toyi-xing/RV32I/docs/simulation_flow_c.md

# C 仿真流程

本文档说明 RV32I 教学核的 C 裸机测试如何编译、生成 IMEM/DMEM 镜像并通过 Verilator 运行。

---

## 1. 仿真命令

当前仓库统一使用 SoC 仿真入口。旧 core-only testbench 和 `sim/pipeline5_c/` 入口已删除。

```bash
sim/soc_c/run_test.sh <test>
sim/soc_c/run_all.sh
```

`<test>` 可以是四位编号或完整 basename，例如：

```bash
sim/soc_c/run_test.sh 0401
sim/soc_c/run_test.sh 0401_control_mix
```

## 2. 与汇编测试的差异

### 2.1 测试程序结构不同

| | 汇编测试 | C 测试 |
|--|---|---|
| 程序入口 | `sw/asm/<test>.S`，手写 `_start` | `sw/c/<test>.c`，搭配 `sw/c_runtime/crt0.S` |
| 链接脚本 | `sw/linker/asm_test.ld` | `sw/linker/c_baremetal.ld` |
| 内存镜像 | 单文件 `.mem`（只含 imem） | 双文件 `_imem.mem` + `_dmem.mem`（`.dmem_image` 段初始数据） |
| dmem 初始化 | 否（RAM 默认全 0） | 是（C 全局变量初始值通过 dmem 镜像加载） |

### 2.2 仿真命令

C 仿真同时加载 imem 和 dmem：

```bash
Vtb_rv32i_soc "+imem=build/soc_c/<test>_imem.mem" "+dmem=build/soc_c/<test>_dmem.mem"
```

## 3. 可用的 C 测试文件

| 文件 | 描述 | 仿真平台 |
|---|---|---|
| `sw/c/0201_c_smoke.c` | 最小冒烟：1+2=3 自检，通过返回 0 | SoC |
| `sw/c/0202_dmem_init.c` | .rodata/.data/.bss 初始化验证 | SoC |
| `sw/c/0401_control_mix.c` | 嵌套循环冒泡排序、函数调用栈、byte/halfword 访存、分支密集路径 | SoC |
| `sw/c/0551_trap_smoke.c` | C trap handler：ECALL 触发、CSR 读取、mret 返回 | SoC |
| `sw/c/0651_soc_mmio_smoke.c` | GPIO OUT/OE/IN 读写、UART 使能/状态查询/TX 发送 | SoC |
| `sw/c/0652_soc_mmio_gpio_uart.c` | GPIO bit 操作、OUT/OE 独立性与 UART 多字符串 | SoC |
| `sw/c/0751_timer_smoke.c` | TIMER0 machine timer interrupt | SoC |
| `sw/c/0752_gpio_irq_basic.c` | GPIO 四类触发、pending/W1C 与 external interrupt | SoC |
| `sw/c/0753_uart_rx_irq.c` | UART RX 注入、RX interrupt、读清与 W1C | SoC |
| `sw/c/0754_external_timer_priority.c` | MEIP/MTIP 同时 pending 时的优先级 | SoC |
| `sw/c/0757_gpio_periodic_irq.c` | 500/2000 拍 GPIO 周期测量与 4:1 比值 | SoC |
| `sw/c/0853_mmio_wait_basic.c` | 固定 PREADY APB 外设基本读写与副作用 | SoC |
| `sw/c/0856_wait_mixed_random_smoke.c` | AXI-Lite DMEM 与 APB MMIO 混合路由 | SoC |

当前 C 回归共 13 个测试，0836 收口结果为 13 passed、0 failed。

## 4. 新建 C 测试

### 4.1 写 .c 文件

在 `sw/c/` 下新建 `<test>.c`，最小骨架：

```c
int main(void)
{
    // 在这里写测试代码

    return 0;  // 0 表示 PASS；非 0 返回值由 crt0.S 转成 FAIL
}
```

几点说明：

- **入口约定**：`crt0.S` 固定提供 `.text.trap` 入口，同时负责初始化栈指针、清零 `.bss`、加载 `.dmem_image` 到 DMEM 基址，然后调用 `main()`。
- **全局变量初始化**：若 C 测试需要在 DMEM 中预置数据，定义全局变量并赋初值即可。链接脚本会将这些初始值收集到 `.dmem_image` 段，仿真启动时 testbench 通过 `$readmemh` 加载到 `axi_lite_ram.mem`。
- **PASS/FAIL 约定**：C 测试由 `crt0.S` 统一写 `DMEM_BASE + 0x100`（即 `0x00040100`）。`main()` 返回 0 时写 1 表示 PASS，返回非 0 时写 2 表示 FAIL。超时（30010 周期）自动判 TIMEOUT。
- **trap 约定**：需要处理 trap 的 C 测试实现 `__trap_handler_c(unsigned int mcause, unsigned int mepc, unsigned int mtval)`。handler 返回值会写入 `mepc`，随后由 runtime 执行 `mret`；普通 C 测试使用默认弱 handler，若意外 trap 则写 FAIL。
- **MMIO 约定**：需要访问 MMIO 外设的测试包含 `sw/include/platform.h`，使用 `mmio_read32`/`mmio_write32` 等封装函数操作寄存器，且必须在 SoC 仿真平台（`sim/soc_c/`）下运行。

### 4.2 生成 Memory Image

```bash
sim/soc_c/05_build_mem.sh <test>
```

执行流程：

1. `gcc` 编译 + 链接（`-T sw/linker/c_baremetal.ld`）→ `.elf`
2. `objdump -d` → `.dump`
3. `objcopy -j .text.init -j .text.trap -j .text` → `_imem.bin` → `_imem.mem`
4. `objcopy -j .dmem_image` → `_dmem.bin` → `_dmem.mem`

输出在 `build/soc_c/` 下。**每次修改 .c 后都需重新运行此脚本。**

### 4.3 运行仿真

```bash
sim/soc_c/06_run_sim.sh <test>
```

正常输出类似：

```
[0] @ 55: PC=0x00000000 Instr=0x00040537   rd=x10 <= 0x00040000
...
PASS after N cycles
DMEM access range: 0x00040200 - 0x0007fffc
Stack max used:    80 bytes
```

`DMEM access range` 统计仿真期间程序实际发起过 load/store 的最小和最大 DMEM 地址，已排除 `TEST_STATUS_ADDR` 的 PASS/FAIL 写入。`Stack max used` 通过 `min(sp)` 估算最大栈深，C 测试由 `crt0.S` 初始化 `sp`，因此这个值通常比 `.mem` 文件大小更能反映运行时栈压力。DMEM 地址范围不等价于真实 RAM 占用，因为中间地址未必都被访问；详细口径见 `docs/08xx/0827 Testbench、commit trace与测试集组织.md`。

## 5. 调试注意事项

- C 测试的 commit trace 比汇编更晚出现，因为 `crt0.S` 在进入 `main()` 前做了栈和 bss 初始化。
- C trap 测试的 commit trace 会额外看到 `trap_entry/trap_return` 打印，以及 runtime 中保存/恢复寄存器的指令。
- `sw/linker/c_baremetal.ld` 中 `__stack_top` 的值和栈指针初始化代码（`crt0.S`）必须一致，否则 `main()` 内的函数调用会异常。
- 全局变量的 dmem 地址可通过 `.map` 文件或 `.dump` 中的符号地址确认。
- RTL 文件由 SoC 仿真脚本自动收集：`rtl/common/*.sv`、`rtl/core/*.sv`、`rtl/bus/axi_lite/*.sv`、`rtl/bus/bridge/*.sv`、`rtl/bus/apb/*.sv`、`rtl/mem/*.sv`、`rtl/periph/*.sv`、`rtl/soc/*.sv`。
