toyi-xing/RV32I/sw/linker/readme.md

# Linker 与内存分配说明

本文说明当前五级流水线核仿真使用的 IMEM/DMEM 地址图，以及 `asm_test.ld`、`c_baremetal.ld` 的分工。

## 当前地址图

RTL 中当前主线使用 `simple_rom` 作为 IMEM、`axi_lite_ram` 作为 DMEM，两者都使用 32-bit word array。当前 `ADDR_WIDTH=16`，因此每块 memory 有 65536 words，即 256 KiB；`simple_ram` 仅保留为 legacy simple-bus 参考。

| 区域 | 起始地址 | 结束地址 | 大小 | 用途 |
|---|---:|---:|---:|---|
| IMEM | `0x0000_0000` | `0x0003_FFFF` | 256 KiB | 指令、trap handler、部分只读内容 |
| DMEM | `0x0004_0000` | `0x0007_FFFF` | 256 KiB | 数据、测试状态、C 栈 |
| MMIO | `0x0008_0000` | `0x0008_FFFF` | 64 KiB | UART/GPIO/TIMER/ACCEL MMIO window |

MMIO window 内已实现外设（ACCEL0 预留）：

| 外设 | Base | 大小 | 当前状态 |
|---|-----:|----:|---|
| GPIO0 | `0x0008_0000` | 256 B | 已实现 OUT/IN/OE、中断扩展 |
| TIMER0 | `0x0008_1000` | 256 B | 已实现 MTIME/MTIMECMP/CTRL |
| UART0 | `0x0008_2000` | 256 B | 已实现 TXDATA/STATUS/CTRL/RXDATA、中断扩展 |
| ACCEL0 | `0x0008_8000` | 4 KiB | 预留，访问 fault |

对应 RTL 常量在 `rtl/common/core_pkg.sv`（IMEM/DMEM）和 `rtl/common/soc_pkg.sv`（MMIO 窗口）：

```systemverilog
IMEM_BASE       = 32'h0000_0000;
DMEM_BASE       = 32'h0004_0000;
IMEM_SIZE_BYTES = 32'h0004_0000;
DMEM_SIZE_BYTES = 32'h0004_0000;
MTVEC_RESET     = IMEM_BASE + 32'h0000_0080;
```

## IMEM 布局

两个 linker script 都采用同一套 IMEM 入口约定：

| 地址/段 | 用途 |
|---|---|
| `0x0000_0000` / `.text.init` | reset 后第一段代码，必须包含 `_start` |
| `0x0000_0080` / `.text.trap` | M-mode direct trap 入口，对齐 `MTVEC_RESET` |
| `.text` | 普通程序代码，放在 `.text.trap` 之后 |

`.text.trap` 使用 `KEEP(*(.text.trap))`，并且即使当前程序没有 handler，也至少保留 4 bytes。这样普通 `.text` 不会占用 `mtvec` 默认入口；如果程序真的定义了 handler，也不会额外插入无意义占位字。

现有汇编和 C runtime 的 `_start` 都是短入口 stub：

```asm
.section .text.init
_start:
    jal x0, test_main

.section .text
test_main:
    ...
```

这种写法让 reset 入口固定在 `0x0`，同时把普通程序主体避开 `0x80` trap vector。需要 trap handler 的汇编程序应显式放到 `.text.trap`：

```asm
.section .text.trap
trap_handler:
    ...
```

## ASM 链接脚本

`asm_test.ld` 面向手写汇编测试。它的目标是尽量直接、透明：

| 段 | 放置区域 | 说明 |
|---|---|---|
| `.text.init` | IMEM | reset stub |
| `.text.trap` | IMEM `0x80` | trap handler |
| `.text` | IMEM | 普通代码 |
| `.rodata` | IMEM | 只读数据 |
| `.data` | DMEM | 已初始化数据 |
| `.bss` | DMEM | 未初始化数据 |

当前汇编测试优先 `#include "platform.h"` 复用 `DMEM_BASE`、`TEST_STATUS_OFFSET`、外设地址和 CSR bit mask 等公共常量。早期测试可能仍直接用 `lui ..., 0x40` 构造 `DMEM_BASE=0x0004_0000`；这种写法只适合底层冒烟或历史测试，后续新增测试应优先使用公共头文件。

## C 链接脚本

`c_baremetal.ld` 面向 C 裸机测试。C 测试使用两个 memory image：

| 镜像 | 来源段 | 加载目标 |
|---|---|---|
| `_imem.mem` | `.text.init/.text.trap/.text` | `simple_rom` |
| `_dmem.mem` | `.dmem_image` | testbench 中的 `axi_lite_ram.mem` |

C 的 DMEM 布局：

| 地址范围 | 用途 |
|---|---|
| `0x0004_0000` - `0x0004_00FF` | 保留 |
| `0x0004_0100` - `0x0004_0103` | `TEST_STATUS_ADDR` |
| `0x0004_0104` - `0x0004_017F` | 定向测试临时数据/错误码保留区 |
| `0x0004_0180` - `0x0004_018F` | `tb_rv32i_soc.sv` 专用 TB command mailbox |
| `0x0004_0190` - `0x0004_01FF` | 保留 |
| `0x0004_0200` 起 | `.rodata/.data` 初始镜像 |
| `.bss` | `NOLOAD`，由 `crt0.S` 进入 `main()` 前清零 |
| `0x0007_E000` - `0x0007_FFFF` | 预留 C 栈，当前 8 KiB |

关键符号：

| 符号 | 含义 |
|---|---|
| `__test_status_addr` | `DMEM_BASE + 0x100`，`crt0.S` 根据 `main()` 返回值写 PASS/FAIL |
| `__c_data_base` | `DMEM_BASE + 0x200`，C 数据初始镜像起点 |
| `__stack_top` | `DMEM_BASE + DMEM_SIZE_BYTES = 0x0008_0000` |
| `__stack_size` | 当前固定为 `0x2000` |
| `__stack_bottom` | `__stack_top - __stack_size = 0x0007_E000` |
| `__trap_vector` | `IMEM_BASE + 0x80` |

`crt0.S` 使用 linker symbol 设置 `sp`、清零 `.bss`，然后调用 `main()`。C 程序自身不应直接写 `TEST_STATUS_ADDR`；它只返回 0 或非 0，由 `crt0.S` 统一写状态字。

C runtime 还固定提供 `.text.trap` 入口。该入口保存寄存器、读取 `mcause/mepc/mtval`，调用弱符号 `__trap_handler_c`，再按 handler 返回值写 `mepc` 并执行 `mret`。普通 C 测试不触发 trap 时不会用到它；需要处理 trap 的测试提供同名强定义即可覆盖默认 FAIL handler。

`TB_CMD_BASE = DMEM_BASE + 0x180` 及其后 16 bytes 只属于当前 `tb/sv/tb_rv32i_soc.sv` 的 directed-test mailbox 协议，不是真实 SoC 地址图，也不属于通用外设 MMIO ABI。当前四个 word 分别用于 GPIO set、GPIO clear、GPIO pulse 和 UART RX；`0x0004_0190` 起不再定义旧 response-delay 命令。具体地址和 helper 定义见 `sw/include/tb_rv32i_soc_test.h`。

## 修改地址图时要同步的地方

如果后续继续调整 IMEM/DMEM 大小或基址，需要一起检查：

- `rtl/common/core_pkg.sv` 的 `IMEM_*`、`DMEM_*` 常量。
- `rtl/mem/simple_rom.sv`、`rtl/mem/axi_lite_ram.sv` 的默认 `ADDR_WIDTH` 是否仍引用公共常量；`simple_ram.sv` 只在 legacy simple-bus 场景需要同步。
- `sw/linker/asm_test.ld` 和 `sw/linker/c_baremetal.ld` 的 `MEMORY`、`__stack_top`、`__test_status_addr` 等符号。
- `sw/include/platform.h` 中的软件侧地址常量；若仍有历史手写汇编直接构造地址，也需要同步检查。
- `sw/include/tb_rv32i_soc_test.h` 中 TB mailbox 地址是否仍落在 linker 保留区内。
- `tb/sv/tb_rv32i_soc.sv` 中 PASS/FAIL 地址和 DMEM/stack 统计。
- `docs/simulation_flow_asm.md` / `docs/simulation_flow_c.md` 中的命令示例和地址说明。
