toyi-xing/RV32I/fpga/fpga_e10_board_resources/3_正点原子E10最小系统板原理图/readme.txt

E10最小系统板IO引脚分配表：E10最小系统板管脚IO引脚分配表
E10_MicroSYS_IO：E10最小系统板TCL格式IO引脚分配，在工程中做IO分配时，可以直接从该文件中拷贝（要注意该TCL文件的端口名称和工程里的端口名是否一致）
E10最小系统板原理图：E10最小系统板原理图

本目录下包含了正点原子E10最小系统板的所有电路原理图,有的文档有多页,请滚动鼠标滚轮查看!!!

		广州市星翼电子科技有限公司
            电话：020-38271790
            传真：020-36773971
	       	购买：http://shop62103354.taobao.com
                  http://shop62057469.taobao.com
            公司网站：www.alientek.com
         	技术论坛：www.openedv.com
