toyi-xing/RV32I/docs/08xx/0821 RV32I最小教学核指令集、编码与译码参考.md

# 0821 RV32I 最小教学核指令集、编码与译码参考

> 文档编号：0821  
> 所属系列：082x RISC-V 最小教学核项目实践  
> 文档定位：第一版 RV32I 教学核的指令、编码、立即数和译码控制参考  
> 前置文档：`0801 RISC-V ISA基础.md`、`0802 RISC-V五级流水线与Hazard.md`、`0820 RISC-V最小教学核设计流程与方案.md`

本文不是完整 RISC-V 规范替代品，而是为了写第一版 RV32I 五级流水线教学核时查表使用。目标是让实现者能快速回答：

1. 第一版到底支持哪些指令。
2. 每条指令属于哪种 type。
3. opcode、funct3、funct7 怎么匹配。
4. 哪些指令读 `rs1/rs2`，哪些指令写 `rd`。
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
