toyi-xing/RV32I/rtl/core/core.sv

//------------------------------------------------------------------------------
// 文件      : rtl/core/core.sv
// 用途      : RV32I 五级流水线教学核顶层。
//
// 综合PPA：
//   - 该顶层使用 yosys 综合器 + 浙芯 55nm 开源工艺库综合结果：
//   - 最终面积 28351.40，其中时序单元 16896.04 (59.60%)
//   - Setup (max) Worst Slack = 17.569 ns  理论上可以跑到 ~411MHz
//   - Hold (min) Worst Slack = 0.125 ns
//   - Total Power = 0.445 W
//
// 规范：
//   - 普通输入端口使用 _i 后缀，普通输出端口使用 _o 后缀。
//   - commit_instr_id_o 为仿真 trace 观察口，沿用 commit_* 分组命名。
//   - 本模块实现 IF/ID/EX/MEM/WB 五级流水线顶层连接。
//   - 外接 imem 和 LSU 数据侧接口，不在 core 内部实例化具体 memory。
//   - 当前 IMEM 仍为固定响应；LSU 数据侧使用单 outstanding req/resp 结构体接口。
//
// 功能：
//   - 连接 pc_reg、if_stage、id_stage、ex_stage、mem_stage、wb_stage、regfile、csr_file 和 trap_ctrl。
//   - 使用 pipeline_pkg 中的 struct 描述四组流水线寄存器承载的数据和控制。
//   - 处理 forwarding、load-use/CSR-use stall 和 branch/JAL/JALR redirect flush。
//   - 支持 MEM backpressure，IMEM 固定响应。
//   - 在 MEM 边界精确接受 trap/MRET，并通过 kill 清除 younger instruction 或终止当前 MEM 指令普通 WB 路径。
//   - 输出 commit trace 和 trap/MRET trace 观察信号，供 testbench 打印和调试使用。
//------------------------------------------------------------------------------

`default_nettype none

module core (
    input  logic                          clk_i,
    input  logic                          rst_n_i,

    input  logic [core_pkg::ILEN-1:0]     imem_rdata_i,         // imem 返回的 32 bit instruction。
    output logic [core_pkg::XLEN-1:0]     imem_addr_o,          // 输出给 imem 的取指地址。

    // 可变延迟访存总线
    input  logic                          lsu_req_ready_i,          // data-side 可以接受本拍 request；valid && !ready 时 MEM 需要保持等待。
    output data_bus_pkg::data_req_t       lsu_req_o,                // LSU load/store request payload。
    input  data_bus_pkg::data_resp_t      lsu_resp_i,               // LSU response，包含 valid/rdata/error。

    // 中断信号输入
    input  logic                          mtip_i,               // 外设的 mtip 中断挂起
    input  logic                          meip_i,               // 外设的 meip 中断挂起

    // WB 指令提交观察
    output logic                          commit_valid_o,       // 当前拍是否有有效指令提交。
    output logic [core_pkg::XLEN-1:0]     commit_pc_o,          // 提交指令的 PC。
    output logic [core_pkg::ILEN-1:0]     commit_instr_o,       // 提交指令的原始 instruction。
    output core_pkg::instr_id_e           commit_instr_id_o,    // 提交指令类型
    output logic                          commit_reg_we_o,      // 提交指令是否写 rd。
    output logic [4:0]                    commit_rd_addr_o,     // 提交指令写回的 rd 编号。
    output logic [core_pkg::XLEN-1:0]     commit_rd_wdata_o,    // 提交指令写回 rd 的数据。

    // trap/MRET 提交观察
    output logic                          trap_valid_o,         // trap entry 有效（异常/中断），不含 MRET。
    output logic [core_pkg::XLEN-1:0]     trap_pc_o,            // 写入 mepc 的 PC；exception 时为 fault PC，interrupt 时为 return PC。
    output logic                          trap_is_interrupt_o,  // 该 trap 是中断。
    output logic [4:0]                    trap_cause_code_o,    // 当前 trap entry 的 cause code，配合 trap_is_interrupt_o 区分异常和中断。
    output logic [core_pkg::XLEN-1:0]     trap_tval_o,          // 异常相关附加值（mtval 写入值）。
    output logic                          trap_return_o,        // MRET 返回事件有效。
    output logic [core_pkg::XLEN-1:0]     trap_redirect_pc_o,   // trap 或 MRET 的跳转目标 PC。

    // 流水线暂停观察
    output logic                          mem_wait_o            // 因 mem wait 导致的流水线暂停
);
    import core_pkg::*;
    import pipeline_pkg::*;
    import data_bus_pkg::*;

    // pc相关信号
    wire [core_pkg::XLEN-1:0] pc;
    wire                      ex_redirect_valid;
    wire [core_pkg::XLEN-1:0] ex_redirect_pc;
    wire                      nontrap_redirect_valid;
    wire [core_pkg::XLEN-1:0] nontrap_redirect_pc;
    wire                      trap_redirect_valid;
    wire [core_pkg::XLEN-1:0] trap_redirect_pc;
    wire                      redirect_valid = trap_redirect_valid | nontrap_redirect_valid;
    wire [core_pkg::XLEN-1:0] redirect_pc    = trap_redirect_valid ? trap_redirect_pc : nontrap_redirect_pc;

    // pipeline_ctrl 输出的非 trap 类 stall/bubble。
    wire stall_pc;
    wire stall_if_id;
    wire stall_id_ex;
    wire stall_ex_mem;
    wire stall_mem_wb;
    wire bubble_ex;

    // pipeline_ctrl 输出普通 redirect flush；trap/MRET kill 由 trap_ctrl 输出。
    wire flush_if_id;
    wire flush_id_ex;

    // trap/MRET kill 信号
    wire kill_if_id;
    wire kill_id_ex;
    wire kill_ex_mem;
    wire kill_mem_wb;

    // 各 valid 信号，中间 data。由中间寄存器寄存
    wire pc_valid;
    wire if_valid, if_id_valid;
    wire id_valid, id_ex_valid;
    wire ex_valid, ex_mem_valid;
    wire mem_valid, mem_wb_valid, mem_wb_commit_valid;
    wire wb_valid;
    pipeline_pkg::if_id_reg_t if_id_data_d;
    pipeline_pkg::if_id_reg_t if_id_data_q;
    pipeline_pkg::id_ex_reg_t id_ex_data_d;
    pipeline_pkg::id_ex_reg_t id_ex_data_q;
    pipeline_pkg::ex_mem_reg_t ex_mem_data_d;
    pipeline_pkg::ex_mem_reg_t ex_mem_data_q;
    pipeline_pkg::mem_wb_reg_t mem_wb_data_d;
    pipeline_pkg::mem_wb_reg_t mem_wb_data_q;

    // GPR
    wire [4:0]                id_rs1_addr;
    wire [4:0]                id_rs2_addr;
    wire [core_pkg::XLEN-1:0] gpr_rs1_rdata;
    wire [core_pkg::XLEN-1:0] gpr_rs2_rdata;
    wire [core_pkg::XLEN-1:0] wb_rd_wdata;
    wire                      wb_rd_we;

    // IF
    wire [core_pkg::XLEN-1:0] if_pc;
    wire [core_pkg::ILEN-1:0] if_instr;
    wire [core_pkg::XLEN-1:0] if_pc_plus4;

    // ID
    wire [4:0]                id_rd_addr;
    wire                      id_uses_rs1;
    wire                      id_uses_rs2;
    wire                      id_illegal_instr;
    core_pkg::alu_op_e        id_alu_op;
    core_pkg::op_a_sel_e      id_op_a_sel;
    core_pkg::op_b_sel_e      id_op_b_sel;
    wire                      id_rd_we;
    core_pkg::wb_sel_e        id_wb_sel;
    wire                      id_mem_re;
    wire                      id_mem_we;
    core_pkg::mem_size_e      id_mem_size;
    wire                      id_mem_unsigned;
    core_pkg::branch_op_e     id_branch_op;
    wire                      id_jump;
    wire                      id_jalr;
    wire [core_pkg::XLEN-1:0] id_imm;
    wire [core_pkg::XLEN-1:0] id_rs1_rdata, id_rs2_rdata;
    core_pkg::instr_id_e      id_instr_id;
    wire                      id_fence;
    wire                      id_mret;
    wire                      id_csr;
    core_pkg::csr_op_e        id_csr_op;
    wire [11:0]               id_csr_addr;
    wire [4:0]                id_csr_uimm;
    wire                      id_csr_uses_rs1;
    wire                      id_csr_writes_rd;
    wire                      id_csr_write_en;
    wire                      id_exception_valid;
    core_pkg::excp_cause_e    id_exception_cause;
    wire [core_pkg::XLEN-1:0] id_exception_tval;

    // forwarding 前递结果 -> EX 操作数
    wire [core_pkg::XLEN-1:0] ex_rs1_op_data;
    wire [core_pkg::XLEN-1:0] ex_rs2_op_data;

    // EX
    wire [core_pkg::XLEN-1:0] ex_alu_result;
    wire [core_pkg::XLEN-1:0] ex_store_data;
    wire                      ex_exception_valid;
    core_pkg::excp_cause_e    ex_exception_cause;
    wire [core_pkg::XLEN-1:0] ex_exception_tval;
    wire [core_pkg::XLEN-1:0] ex_csr_operand;
    wire                      ex_mret;
    wire [core_pkg::XLEN-1:0] ex_next_pc;

    // MEM
    wire                      mem_wait;
    wire [core_pkg::XLEN-1:0] mem_load_data;
    wire                      mem_exception_valid;
    core_pkg::excp_cause_e    mem_exception_cause;
    wire [core_pkg::XLEN-1:0] mem_exception_tval;

    // CSR 信号
    wire                      mem_csr_valid;    // 当前 MEM 阶段的 csr 指令控制信号
    wire [core_pkg::XLEN-1:0] mem_csr_rdata;
    wire                      mem_csr_illegal;
    wire [core_pkg::XLEN-1:0] csr_mstatus;
    wire [core_pkg::XLEN-1:0] csr_mstatus_commit;
    wire [core_pkg::XLEN-1:0] csr_mie;
    wire [core_pkg::XLEN-1:0] csr_mie_commit;
    wire [core_pkg::XLEN-1:0] csr_mtvec;        // 恒为当前对于 csr 寄存器值
    wire [core_pkg::XLEN-1:0] csr_mtvec_commit;
    wire [core_pkg::XLEN-1:0] csr_mepc;
    wire [core_pkg::XLEN-1:0] csr_mip;

    // 系统级 trap 信号
    wire                      trap_valid;
    wire [core_pkg::XLEN-1:0] trap_pc;
    wire                      trap_is_interrupt;
    wire [4:0]                trap_cause_code;
    wire [core_pkg::XLEN-1:0] trap_tval;
    wire                      mret_valid;

    // WB 随指令输出 -> commit
    wire [core_pkg::ILEN-1:0] wb_instr          = mem_wb_data_q.instr;
    core_pkg::instr_id_e      wb_instr_id;
    assign                    wb_instr_id       = mem_wb_data_q.instr_id;
    wire [core_pkg::XLEN-1:0] wb_pc             = mem_wb_data_q.pc;
    wire [4:0]                wb_rd_addr        = mem_wb_data_q.rd_addr;

    pc_reg u_pc_reg(
        .clk_i              (clk_i),
        .rst_n_i            (rst_n_i),

        .pc_plus4_i         (if_pc_plus4),
        .redirect_pc_i      (redirect_pc),
        .redirect_valid_i   (redirect_valid),
        .stall_pc_i         (stall_pc), // if 要 stall 一拍，让 pc 保持不变

        .pc_o               (pc),
        .pc_valid_o         (pc_valid)
    );

    if_stage u_if_stage (
        .pc_i           (pc),
        .imem_rdata_i   (imem_rdata_i),
        .pc_valid_i     (pc_valid),

        .imem_addr_o    (imem_addr_o),
        .if_pc_o        (if_pc),
        .if_pc_plus4_o  (if_pc_plus4),
        .if_instr_o     (if_instr),
        .if_valid_o     (if_valid)
    );

    pipe_reg_if_id u_pipe_reg_if_id (
        .clk_i      (clk_i),
        .rst_n_i    (rst_n_i),

        .data_i     (if_id_data_d),
        .valid_i    (if_valid),
        .kill_i     (kill_if_id),       // trap control hazard
        .flush_i    (flush_if_id),      // base control hazard
        .stall_i    (stall_if_id),      // late_result_use_stall 时 id 要 stall 一拍

        .data_o     (if_id_data_q),
        .valid_o    (if_id_valid)
    );

    // IF/ID 输入组包。后续若取指侧增加 kill/valid 修正，在这里改。
    assign if_id_data_d.pc       = if_pc;
    assign if_id_data_d.instr    = if_instr;
    assign if_id_data_d.pc_plus4 = if_pc_plus4;

    id_stage u_id_stage (
        .if_valid_i     (if_id_valid),
        .if_instr_i     (if_id_data_q.instr),
        .rs1_rdata_i    (gpr_rs1_rdata),
        .rs2_rdata_i    (gpr_rs2_rdata),

        .rs1_addr_o     (id_rs1_addr),
        .rs2_addr_o     (id_rs2_addr),
        .rd_addr_o      (id_rd_addr),

        .instr_id_o     (id_instr_id),     // 调试用,送到流水线结束

        .uses_rs1_o     (id_uses_rs1),
        .uses_rs2_o     (id_uses_rs2),

        .alu_op_o       (id_alu_op),
        .op_a_sel_o     (id_op_a_sel),
        .op_b_sel_o     (id_op_b_sel),

        .reg_we_o       (id_rd_we),
        .wb_sel_o       (id_wb_sel),

        .mem_re_o       (id_mem_re),
        .mem_we_o       (id_mem_we),
        .mem_size_o     (id_mem_size),
        .mem_unsigned_o (id_mem_unsigned),

        .branch_op_o    (id_branch_op),

        .jump_o         (id_jump),
        .jalr_o         (id_jalr),
        .fence_o        (id_fence),
        .mret_o         (id_mret),

        .csr_o              (id_csr),
        .csr_op_o           (id_csr_op),
        .csr_addr_o         (id_csr_addr),
        .csr_uimm_o         (id_csr_uimm),
        .csr_uses_rs1_o     (id_csr_uses_rs1),
        .csr_writes_rd_o    (id_csr_writes_rd),     // csr 指令写 gpr
        .csr_write_en_o     (id_csr_write_en),      // csr 指令写 csr

        .exception_valid_o  (id_exception_valid),
        .exception_cause_o  (id_exception_cause),
        .exception_tval_o   (id_exception_tval),

        .illegal_instr_o(id_illegal_instr),

        .id_imm_o       (id_imm),

        .id_valid_o     (id_valid),
        .id_rs1_rdata_o (id_rs1_rdata),
        .id_rs2_rdata_o (id_rs2_rdata)
    );

    regfile #(.BYPASS_EN(1)) u_regfile (
        .clk_i          (clk_i),
        .rst_n_i        (rst_n_i),

        .rs1_addr_i     (id_rs1_addr),
        .rs1_rdata_o    (gpr_rs1_rdata),

        .rs2_addr_i     (id_rs2_addr),
        .rs2_rdata_o    (gpr_rs2_rdata),

        .we_i           (wb_rd_we),
        .rd_addr_i      (wb_rd_addr),
        .rd_wdata_i     (wb_rd_wdata)
    );

    // forwarding，处理 RAW 时 EX/MEM -> EX 和 MEM/WB -> EX
    forwarding_unit u_forwarding_unit (
        .id_ex_valid_i      (id_ex_valid),
        .id_ex_rs1_addr_i   (id_ex_data_q.rs1_addr),
        .id_ex_rs2_addr_i   (id_ex_data_q.rs2_addr),
        .id_ex_uses_rs1_i   (id_ex_data_q.uses_rs1),
        .id_ex_uses_rs2_i   (id_ex_data_q.uses_rs2),

        .ex_mem_valid_i     (ex_mem_valid),
        .ex_mem_rd_addr_i   (ex_mem_data_q.rd_addr),
        .ex_mem_reg_we_i    (ex_mem_data_q.reg_we),
        .ex_mem_load_re_i   (ex_mem_data_q.mem_re),
        .ex_mem_csr_re_i    (ex_mem_data_q.csr_writes_rd),

        .mem_wb_valid_i     (mem_wb_valid),
        .mem_wb_rd_addr_i   (mem_wb_data_q.rd_addr),
        .mem_wb_reg_we_i    (mem_wb_data_q.reg_we),

        .id_ex_rs1_rdata_i  (id_ex_data_q.rs1_rdata),
        .id_ex_rs2_rdata_i  (id_ex_data_q.rs2_rdata),
        .ex_mem_wb_sel_i    (ex_mem_data_q.wb_sel),
        .ex_mem_alu_result_i(ex_mem_data_q.alu_result),
        .ex_mem_pc_plus4_i  (ex_mem_data_q.pc_plus4),
        .ex_mem_imm_i       (ex_mem_data_q.imm),
        .mem_wb_wdata_i     (wb_rd_wdata),

        .rs1_fwd_o          (ex_rs1_op_data),
        .rs2_fwd_o          (ex_rs2_op_data)
    );

    pipe_reg_id_ex u_pipe_reg_id_ex (
        .clk_i      (clk_i),
        .rst_n_i    (rst_n_i),

        .data_i     (id_ex_data_d),
        .valid_i    (id_valid),
        .kill_i     (kill_id_ex),     // trap control hazard
        .flush_i    (flush_id_ex),    // base control hazard
        .bubble_i   (bubble_ex),
        .stall_i    (stall_id_ex),

        .data_o     (id_ex_data_q),
        .valid_o    (id_ex_valid)
    );

    // ID/EX 输入组包。控制信号从 ID 生成，随指令进入 EX。
    assign id_ex_data_d.rs1_addr      = id_rs1_addr;
    assign id_ex_data_d.rs2_addr      = id_rs2_addr;
    assign id_ex_data_d.uses_rs1      = id_uses_rs1;
    assign id_ex_data_d.uses_rs2      = id_uses_rs2;
    assign id_ex_data_d.illegal_instr = id_illegal_instr;
    assign id_ex_data_d.instr_id      = id_instr_id;

    assign id_ex_data_d.rd_addr       = id_rd_addr;
    assign id_ex_data_d.alu_op        = id_alu_op;
    assign id_ex_data_d.op_a_sel      = id_op_a_sel;
    assign id_ex_data_d.op_b_sel      = id_op_b_sel;
    assign id_ex_data_d.reg_we        = id_rd_we;
    assign id_ex_data_d.wb_sel        = id_wb_sel;
    assign id_ex_data_d.mem_re        = id_mem_re;
    assign id_ex_data_d.mem_we        = id_mem_we;
    assign id_ex_data_d.mem_size      = id_mem_size;
    assign id_ex_data_d.mem_unsigned  = id_mem_unsigned;
    assign id_ex_data_d.branch_op     = id_branch_op;
    assign id_ex_data_d.jump          = id_jump;
    assign id_ex_data_d.jalr          = id_jalr;
    assign id_ex_data_d.imm           = id_imm;
    assign id_ex_data_d.rs1_rdata     = id_rs1_rdata;
    assign id_ex_data_d.rs2_rdata     = id_rs2_rdata;

    assign id_ex_data_d.pc            = if_id_data_q.pc;        // 此类为中间寄存器直接透传
    assign id_ex_data_d.pc_plus4      = if_id_data_q.pc_plus4;
    assign id_ex_data_d.instr         = if_id_data_q.instr;

    assign id_ex_data_d.exception_valid = id_exception_valid;
    assign id_ex_data_d.exception_cause = id_exception_cause;
    assign id_ex_data_d.exception_tval  = id_exception_tval;
    assign id_ex_data_d.fence           = id_fence;
    assign id_ex_data_d.mret            = id_mret;
    assign id_ex_data_d.csr             = id_csr;
    assign id_ex_data_d.csr_op          = id_csr_op;
    assign id_ex_data_d.csr_addr        = id_csr_addr;
    assign id_ex_data_d.csr_uimm        = id_csr_uimm;
    assign id_ex_data_d.csr_uses_rs1    = id_csr_uses_rs1;
    assign id_ex_data_d.csr_writes_rd   = id_csr_writes_rd;
    assign id_ex_data_d.csr_write_en    = id_csr_write_en;

    ex_stage u_ex_stage (
        .valid_i            (id_ex_valid),

        .pc_i               (id_ex_data_q.pc),
        .pc_plus4_i         (id_ex_data_q.pc_plus4),
        .rs1_data_i         (ex_rs1_op_data),
        .rs2_data_i         (ex_rs2_op_data),
        .imm_i              (id_ex_data_q.imm),
        .alu_op_i           (id_ex_data_q.alu_op),
        .op_a_sel_i         (id_ex_data_q.op_a_sel),
        .op_b_sel_i         (id_ex_data_q.op_b_sel),
        .branch_op_i        (id_ex_data_q.branch_op),
        .jump_i             (id_ex_data_q.jump),
        .jalr_i             (id_ex_data_q.jalr),

        .exception_valid_i  (id_ex_data_q.exception_valid),
        .exception_cause_i  (id_ex_data_q.exception_cause),
        .exception_tval_i   (id_ex_data_q.exception_tval),
        .csr_i              (id_ex_data_q.csr),
        .csr_op_i           (id_ex_data_q.csr_op),
        .csr_uimm_i         (id_ex_data_q.csr_uimm),
        .mret_i             (id_ex_data_q.mret),

        .valid_o            (ex_valid),
        .alu_result_o       (ex_alu_result),
        .store_data_o       (ex_store_data),
        .redirect_valid_o   (ex_redirect_valid),
        .redirect_pc_o      (ex_redirect_pc),

        .exception_valid_o  (ex_exception_valid),
        .exception_cause_o  (ex_exception_cause),
        .exception_tval_o   (ex_exception_tval),
        .csr_operand_o      (ex_csr_operand),
        .mret_o             (ex_mret),
        .next_pc_o          (ex_next_pc)
    );

    pipe_reg_ex_mem u_pipe_reg_ex_mem (
        .clk_i      (clk_i),
        .rst_n_i    (rst_n_i),

        .data_i     (ex_mem_data_d),
        .valid_i    (ex_valid),
        .kill_i     (kill_ex_mem),     // trap control hazard
        .stall_i    (stall_ex_mem),

        .data_o     (ex_mem_data_q),
        .valid_o    (ex_mem_valid)
    );

    // EX/MEM 输入组包。EX 结果和仍需后传的控制信号在这里汇总。
    assign ex_mem_data_d.illegal_instr = id_ex_data_q.illegal_instr;    // 此类为中间寄存器透传
    assign ex_mem_data_d.instr_id      = id_ex_data_q.instr_id;

    assign ex_mem_data_d.alu_result    = ex_alu_result;     // 此类为上一阶段结果
    assign ex_mem_data_d.store_data    = ex_store_data;

    assign ex_mem_data_d.mem_re        = id_ex_data_q.mem_re;
    assign ex_mem_data_d.mem_we        = id_ex_data_q.mem_we;
    assign ex_mem_data_d.mem_size      = id_ex_data_q.mem_size;
    assign ex_mem_data_d.mem_unsigned  = id_ex_data_q.mem_unsigned;
    assign ex_mem_data_d.wb_sel        = id_ex_data_q.wb_sel;
    assign ex_mem_data_d.reg_we        = id_ex_data_q.reg_we;
    assign ex_mem_data_d.pc_plus4      = id_ex_data_q.pc_plus4;
    assign ex_mem_data_d.imm           = id_ex_data_q.imm;
    assign ex_mem_data_d.rd_addr       = id_ex_data_q.rd_addr;
    assign ex_mem_data_d.instr         = id_ex_data_q.instr;
    assign ex_mem_data_d.pc            = id_ex_data_q.pc;

    assign ex_mem_data_d.exception_valid = ex_exception_valid;
    assign ex_mem_data_d.exception_cause = ex_exception_cause;
    assign ex_mem_data_d.exception_tval  = ex_exception_tval;
    assign ex_mem_data_d.fence           = id_ex_data_q.fence;
    assign ex_mem_data_d.mret            = ex_mret;
    assign ex_mem_data_d.csr             = id_ex_data_q.csr;
    assign ex_mem_data_d.csr_op          = id_ex_data_q.csr_op;
    assign ex_mem_data_d.csr_addr        = id_ex_data_q.csr_addr;
    assign ex_mem_data_d.csr_operand     = ex_csr_operand;
    assign ex_mem_data_d.csr_writes_rd   = id_ex_data_q.csr_writes_rd;
    assign ex_mem_data_d.csr_write_en    = id_ex_data_q.csr_write_en;
    assign ex_mem_data_d.next_pc         = ex_next_pc;

    mem_stage u_mem_stage (
        .clk_i                  (clk_i),
        .rst_n_i                (rst_n_i),

        .valid_i                (ex_mem_valid),
        .alu_result_i           (ex_mem_data_q.alu_result),
        .store_data_i           (ex_mem_data_q.store_data),
        .mem_re_i               (ex_mem_data_q.mem_re),
        .mem_we_i               (ex_mem_data_q.mem_we),
        .mem_size_i             (ex_mem_data_q.mem_size),
        .mem_unsigned_i         (ex_mem_data_q.mem_unsigned),

        .valid_o                (mem_valid),
        .load_data_o            (mem_load_data),

        .exception_valid_i      (ex_mem_data_q.exception_valid),
        .exception_cause_i      (ex_mem_data_q.exception_cause),
        .exception_tval_i       (ex_mem_data_q.exception_tval),

        .exception_valid_o      (mem_exception_valid),
        .exception_cause_o      (mem_exception_cause),
        .exception_tval_o       (mem_exception_tval),

        .lsu_req_ready_i        (lsu_req_ready_i),
        .lsu_req_o              (lsu_req_o),
        .lsu_resp_i             (lsu_resp_i),

        .mem_wait_o             (mem_wait),

        .mem_misaligned_o       (),     // 可作为调试信号使用，暂不接
        .load_misaligned_o      (),
        .store_misaligned_o     (),
        .mem_access_fault_o     (),
        .load_access_fault_o    (),
        .store_access_fault_o   (),
        .transaction_complete_o (),
        .mem_complete_o         ()
    );

    // 与 mem_stage “并连”,mem_valid 只是防御性写法，实际上 CSR 指令与访存指令互斥，用 ex_mem_valid 也可且可能更快
    assign mem_csr_valid = mem_valid & ex_mem_data_q.csr & ~mem_exception_valid;
    csr_file u_csr_file (
        .clk_i              (clk_i),
        .rst_n_i            (rst_n_i),

        .csr_valid_i        (mem_csr_valid),
        .csr_op_i           (ex_mem_data_q.csr_op),
        .csr_addr_i         (ex_mem_data_q.csr_addr),
        .csr_operand_i      (ex_mem_data_q.csr_operand),
        .csr_write_en_i     (ex_mem_data_q.csr_write_en),

        .csr_rdata_o        (mem_csr_rdata),
        .csr_illegal_o      (mem_csr_illegal),

        .trap_valid_i       (trap_valid),
        .trap_pc_i          (trap_pc),
        .trap_is_interrupt_i(trap_is_interrupt),
        .trap_cause_code_i  (trap_cause_code),
        .trap_tval_i        (trap_tval),

        .mret_valid_i       (mret_valid),

        .mtip_i             (mtip_i),
        .meip_i             (meip_i),

        .mstatus_o          (csr_mstatus),
        .mstatus_commit_o   (csr_mstatus_commit),
        .mie_o              (csr_mie),
        .mie_commit_o       (csr_mie_commit),
        .mtvec_o            (csr_mtvec),
        .mtvec_commit_o     (csr_mtvec_commit),
        .mepc_o             (csr_mepc),
        .mip_o              (csr_mip)
    );

    trap_ctrl u_trap_ctrl (
        .mem_valid_i                (mem_valid),                // 访存完成后才能明确且允许 trap
        .mem_pc_i                   (ex_mem_data_q.pc),         // 本指令的 pc
        .mem_instr_i                (ex_mem_data_q.instr),
        .mem_mret_i                 (ex_mem_data_q.mret),

        .mem_exception_valid_i      (mem_exception_valid),
        .mem_exception_cause_i      (mem_exception_cause),
        .mem_exception_tval_i       (mem_exception_tval),

        .mem_csr_valid_i            (mem_csr_valid),
        .mem_csr_illegal_i          (mem_csr_illegal),

        .csr_mtvec_i                (csr_mtvec),
        .csr_mepc_i                 (csr_mepc),

        .mem_interrupt_return_pc_i  (ex_mem_data_q.next_pc),    // 本指令的下一个 pc
        .csr_mstatus_i              (csr_mstatus),
        .csr_mie_i                  (csr_mie),
        .csr_mip_i                  (csr_mip),
        .mem_csr_write_en_i         (ex_mem_data_q.csr_write_en),
        .csr_mstatus_commit_i       (csr_mstatus_commit),
        .csr_mie_commit_i           (csr_mie_commit),
        .csr_mtvec_commit_i         (csr_mtvec_commit),

        .trap_valid_o               (trap_valid),
        .trap_pc_o                  (trap_pc),      // 写入 mepc 的 PC：exception 为 fault PC，interrupt 为 return PC。
                                                    // 普通 interrupt 使用 next_pc，MRET+interrupt 使用当前 mepc。
        .trap_is_interrupt_o        (trap_is_interrupt),
        .trap_cause_code_o          (trap_cause_code),
        .trap_tval_o                (trap_tval),

        .mret_valid_o               (mret_valid),

        .redirect_valid_o           (trap_redirect_valid),
        .redirect_pc_o              (trap_redirect_pc),

        .kill_if_id_o               (kill_if_id),
        .kill_id_ex_o               (kill_id_ex),
        .kill_ex_mem_o              (kill_ex_mem),
        .kill_mem_wb_o              (kill_mem_wb)
    );

    // trap/MRET 随流水线在 MEM 边界精确提交，这里只把观察信号导出给 testbench。
    assign trap_valid_o         = trap_valid;
    assign trap_pc_o            = trap_pc;
    assign trap_is_interrupt_o  = trap_is_interrupt;
    assign trap_cause_code_o    = trap_cause_code;
    assign trap_tval_o          = trap_tval;
    assign trap_return_o        = mret_valid;
    assign trap_redirect_pc_o   = trap_redirect_pc;

    // pipeline_ctrl 统一整合 late-result-use stall、non-trap redirect flush 和 MEM backpressure。
    pipeline_ctrl u_pipeline_ctrl (
        .if_id_valid_i              (if_id_valid),
        .id_rs1_addr_i              (id_rs1_addr),
        .id_rs2_addr_i              (id_rs2_addr),
        .id_uses_rs1_i              (id_uses_rs1),
        .id_uses_rs2_i              (id_uses_rs2),

        .id_ex_valid_i              (id_ex_valid),
        .id_ex_rd_addr_i            (id_ex_data_q.rd_addr),
        .id_ex_reg_we_i             (id_ex_data_q.reg_we),
        .id_ex_load_re_i            (id_ex_data_q.mem_re),
        .id_ex_csr_re_i             (id_ex_data_q.csr_writes_rd),

        .mem_wait_i                 (mem_wait),

        .ex_redirect_valid_i        (ex_redirect_valid),
        .ex_redirect_pc_i           (ex_redirect_pc),

        .nontrap_redirect_valid_o   (nontrap_redirect_valid),
        .nontrap_redirect_pc_o      (nontrap_redirect_pc),

        .stall_pc_o                 (stall_pc),
        .stall_if_id_o              (stall_if_id),
        .stall_id_ex_o              (stall_id_ex),
        .stall_ex_mem_o             (stall_ex_mem),
        .stall_mem_wb_o             (stall_mem_wb),

        .bubble_ex_o                (bubble_ex),
        .flush_if_id_o              (flush_if_id),
        .flush_id_ex_o              (flush_id_ex)
    );

    pipe_reg_mem_wb u_pipe_reg_mem_wb (
        .clk_i          (clk_i),
        .rst_n_i        (rst_n_i),

        .data_i         (mem_wb_data_d),
        .valid_i        (mem_valid),
        .kill_i         (kill_mem_wb),     // trap control hazard，终止该指令生命周期（已被 trap 提交）
        .stall_i        (stall_mem_wb),    // MEM wait 还要 stall MEM/WB，供 forwarding 的 MEM/WB -> EX，但续额外处理重复提交问题

        .data_o         (mem_wb_data_q),
        .valid_o        (mem_wb_valid),
        .commit_valid_o (mem_wb_commit_valid)   // 一次有效指令只能提交一次
    );

    // MEM/WB 输入组包。WB 使用这里保存的最终写回选择和数据。
    assign mem_wb_data_d.illegal_instr = ex_mem_data_q.illegal_instr;
    assign mem_wb_data_d.instr_id      = ex_mem_data_q.instr_id;

    assign mem_wb_data_d.load_data     = mem_load_data;

    assign mem_wb_data_d.reg_we        = ex_mem_data_q.reg_we;
    assign mem_wb_data_d.wb_sel        = ex_mem_data_q.wb_sel;
    assign mem_wb_data_d.alu_result    = ex_mem_data_q.alu_result;
    assign mem_wb_data_d.pc_plus4      = ex_mem_data_q.pc_plus4;
    assign mem_wb_data_d.imm           = ex_mem_data_q.imm;
    assign mem_wb_data_d.rd_addr       = ex_mem_data_q.rd_addr;
    assign mem_wb_data_d.instr         = ex_mem_data_q.instr;
    assign mem_wb_data_d.pc            = ex_mem_data_q.pc;

    assign mem_wb_data_d.csr_rdata     = mem_csr_rdata;

    wb_stage u_wb_stage (
        .valid_i        (mem_wb_commit_valid),  // 指令一旦流入 wb 阶段比被提交，因此副作用、提交 valid 需要用脉冲 mem_wb_commit_valid
        .reg_we_i       (mem_wb_data_q.reg_we),
        .rd_addr_i      (mem_wb_data_q.rd_addr),
        .wb_sel_i       (mem_wb_data_q.wb_sel),
        .alu_result_i   (mem_wb_data_q.alu_result),
        .load_data_i    (mem_wb_data_q.load_data),
        .pc_plus4_i     (mem_wb_data_q.pc_plus4),
        .imm_i          (mem_wb_data_q.imm),
        .csr_rdata_i    (mem_wb_data_q.csr_rdata),

        .valid_o        (wb_valid),
        .reg_we_o       (wb_rd_we),
        .wb_wdata_o     (wb_rd_wdata)
    );

    assign commit_valid_o    = wb_valid;
    assign commit_pc_o       = wb_pc;
    assign commit_instr_o    = wb_instr;
    assign commit_instr_id_o = wb_instr_id;
    assign commit_reg_we_o   = wb_rd_we;
    assign commit_rd_addr_o  = wb_rd_addr;
    assign commit_rd_wdata_o = wb_rd_wdata;

    assign mem_wait_o = mem_wait;

endmodule

`default_nettype wire
