toyi-xing/RV32I/rtl/soc/rv32i_soc.sv

//------------------------------------------------------------------------------
// 文件      : rtl/soc/rv32i_soc.sv
// 用途      : RV32I 教学核最小 SoC 平台顶层。
//
// 规范：
//   - 普通输入端口使用 _i 后缀，普通输出端口使用 _o 后缀。
//   - 本模块集成固定响应 IMEM、core-side simple data bus 和 AXI-Lite/APB 数据子系统。
//   - CPU core、外置 IMEM、外置 AXI-Lite DMEM 和内部 APB MMIO 外设在本层连接。
//   - data 观察口按 request/response 结构体分组，避免混淆 request 意图和 response completion。
//
// 功能：
//   - 实例化 core 作为 CPU core。
//   - 透出固定响应 IMEM 端口，由 testbench 或上层 wrapper 连接 simple_rom/ROM model。
//   - 实例化 data_subsystem，把 core simple request 路由到外置 AXI-Lite DMEM 或内部 APB 外设。
//   - 将 data_subsystem response valid/rdata/error 接回 core LSU response 端口。
//   - 汇总 GPIO0/UART0 中断为 MEIP，将 TIMER0 中断作为 MTIP 接入 core。
//   - 透传 commit/trap、GPIO、UART、interrupt 和 data access 观察信号给 testbench。
//------------------------------------------------------------------------------

`default_nettype none

module rv32i_soc (
    input  logic                          clk_i,
    input  logic                          rst_n_i,

    output logic [core_pkg::XLEN-1:0]     imem_addr_o,           // 取指 byte address，连接外置固定响应 IMEM。
    input  logic [core_pkg::ILEN-1:0]     imem_rdata_i,          // 外置 IMEM 返回的 instruction。

    // ----------------------------以下连接外置 DMEM 和外设激励-----------------------------------
    output axi_lite_pkg::axi_lite_req_t   dmem_axi_req_o,        // 发往外置 DMEM AXI-Lite slave 的 request。
    input  axi_lite_pkg::axi_lite_resp_t  dmem_axi_resp_i,       // 外置 DMEM AXI-Lite slave 的 response。

    input  logic [31:0]                   gpio0_in_i,            // GPIO0 输入引脚采样值。
    output logic [31:0]                   gpio0_out_o,           // GPIO0 输出寄存器值。
    output logic [31:0]                   gpio0_oe_o,            // GPIO0 输出使能寄存器值。

    output logic                          uart0_tx_valid_o,      // UART0 TX event 有效脉冲。
    output logic [7:0]                    uart0_tx_data_o,       // UART0 TX event 对应字节。
    input  logic                          uart0_rx_valid_i,      // UART0 RX event 脉冲。
    input  logic [7:0]                    uart0_rx_data_i,       // UART0 RX event 对应字节。

    // ----------------------------以下为 commit/观察口-----------------------------------------
    // data request/response 观察口；load/store 既可能访问 DMEM，也可能访问外设寄存器。
    output logic                          data_req_ready_o,      // data-side 握手：本拍可接受 request。
    output data_bus_pkg::data_req_t       data_req_o,            // core 发起的 LSU request。
    output data_bus_pkg::data_resp_t      data_resp_o,           // data-side response。


    output logic                          dmem_access_o,         // 本拍 data access 是否命中 DMEM。
    output logic                          mmio_access_o,         // 本拍 data access 是否命中已实现 MMIO。
    output logic                          undefined_access_o,    // 本拍 data access 是否命中未实现或未映射区域。

    // 指令提交
    output logic                          commit_valid_o,        // 当前拍是否有有效指令提交。
    output logic [core_pkg::XLEN-1:0]     commit_pc_o,           // 提交指令的 PC。
    output logic [core_pkg::ILEN-1:0]     commit_instr_o,        // 提交指令的原始 instruction。
    output core_pkg::instr_id_e           commit_instr_id_o,     // 提交指令类型。
    output logic                          commit_reg_we_o,       // 提交指令是否写 rd。
    output logic [4:0]                    commit_rd_addr_o,      // 提交指令写回的 rd 编号。
    output logic [core_pkg::XLEN-1:0]     commit_rd_wdata_o,     // 提交指令写回 rd 的数据。

    // trap 提交
    output logic                          trap_valid_o,          // trap entry 有效（异常/中断），不含 MRET。
    output logic [core_pkg::XLEN-1:0]     trap_pc_o,             // 发生异常/中断时的指令 PC。
    output logic                          trap_is_interrupt_o,   // 该 trap 是中断。
    output logic [4:0]                    trap_cause_code_o,     // 当前 trap entry 的 cause code，配合 trap_is_interrupt_o 区分异常和中断。
    output logic [core_pkg::XLEN-1:0]     trap_tval_o,           // 异常相关附加值。
    output logic                          trap_return_o,         // MRET 返回事件有效。
    output logic [core_pkg::XLEN-1:0]     trap_redirect_pc_o,    // trap 或 MRET 的跳转目标 PC。

    // 流水线暂停观察
    output logic                          mem_wait_o,            // 因 mem wait 导致的流水线暂停

    // 中断观察
    output logic                          gpio0_irq_o,           // GPIO0 中断。
    output logic                          uart0_irq_o,           // UART0 中断。
    output logic                          timer0_irq_o,          // TIMER0 中断（MTIP）。
    output logic                          meip_o,                // MEIP = gpio0_irq_o | uart0_irq_o。
    output logic                          mtip_o                 // MTIP = timer0_irq_o。
);
    import data_bus_pkg::*;

    // interrupt 汇总
    wire   meip   = gpio0_irq_o | uart0_irq_o;
    wire   mtip   = timer0_irq_o;
    assign meip_o = meip;
    assign mtip_o = mtip;

    core u_core (
        .clk_i                  (clk_i),
        .rst_n_i                (rst_n_i),

        .imem_rdata_i           (imem_rdata_i),
        .imem_addr_o            (imem_addr_o),

        .lsu_req_ready_i        (data_req_ready_o),
        .lsu_req_o              (data_req_o),
        .lsu_resp_i             (data_resp_o),

        .mtip_i                 (mtip),
        .meip_i                 (meip),

        .commit_valid_o         (commit_valid_o),
        .commit_pc_o            (commit_pc_o),
        .commit_instr_o         (commit_instr_o),
        .commit_instr_id_o      (commit_instr_id_o),
        .commit_reg_we_o        (commit_reg_we_o),
        .commit_rd_addr_o       (commit_rd_addr_o),
        .commit_rd_wdata_o      (commit_rd_wdata_o),

        .trap_valid_o           (trap_valid_o),
        .trap_pc_o              (trap_pc_o),
        .trap_is_interrupt_o    (trap_is_interrupt_o),
        .trap_cause_code_o      (trap_cause_code_o),
        .trap_tval_o            (trap_tval_o),
        .trap_return_o          (trap_return_o),
        .trap_redirect_pc_o     (trap_redirect_pc_o),

        .mem_wait_o             (mem_wait_o)
    );

    data_subsystem u_data_subsystem (
        .clk_i                 (clk_i),
        .rst_n_i               (rst_n_i),

        .core_req_ready_o      (data_req_ready_o),
        .core_req_i            (data_req_o),
        .core_resp_o           (data_resp_o),

        .dmem_axi_req_o        (dmem_axi_req_o),
        .dmem_axi_resp_i       (dmem_axi_resp_i),

        .gpio0_in_i            (gpio0_in_i),
        .gpio0_out_o           (gpio0_out_o),
        .gpio0_oe_o            (gpio0_oe_o),

        .uart0_tx_valid_o      (uart0_tx_valid_o),
        .uart0_tx_data_o       (uart0_tx_data_o),
        .uart0_rx_valid_i      (uart0_rx_valid_i),
        .uart0_rx_data_i       (uart0_rx_data_i),

        .gpio0_irq_o           (gpio0_irq_o),
        .uart0_irq_o           (uart0_irq_o),
        .timer0_irq_o          (timer0_irq_o),

        .dmem_access_o         (dmem_access_o),
        .mmio_access_o         (mmio_access_o),
        .undefined_access_o    (undefined_access_o)
    );

endmodule

`default_nettype wire
